meadiode/EMES/images/housing_cad_02.png

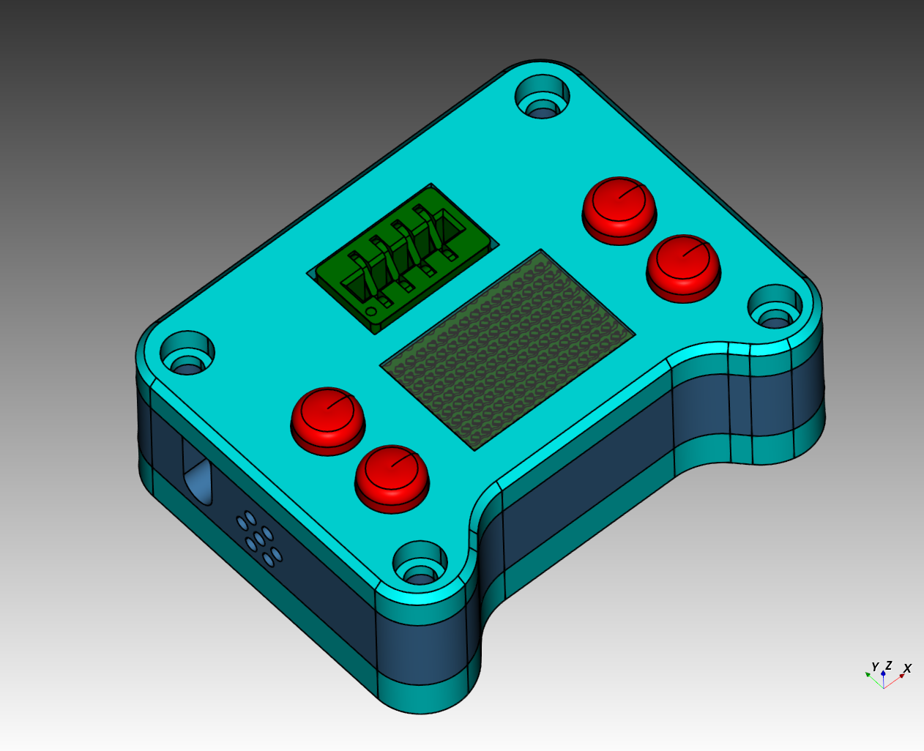
images/housing_cad_02.png
